raszpl/386RC-16/386RC-16 diagram.png

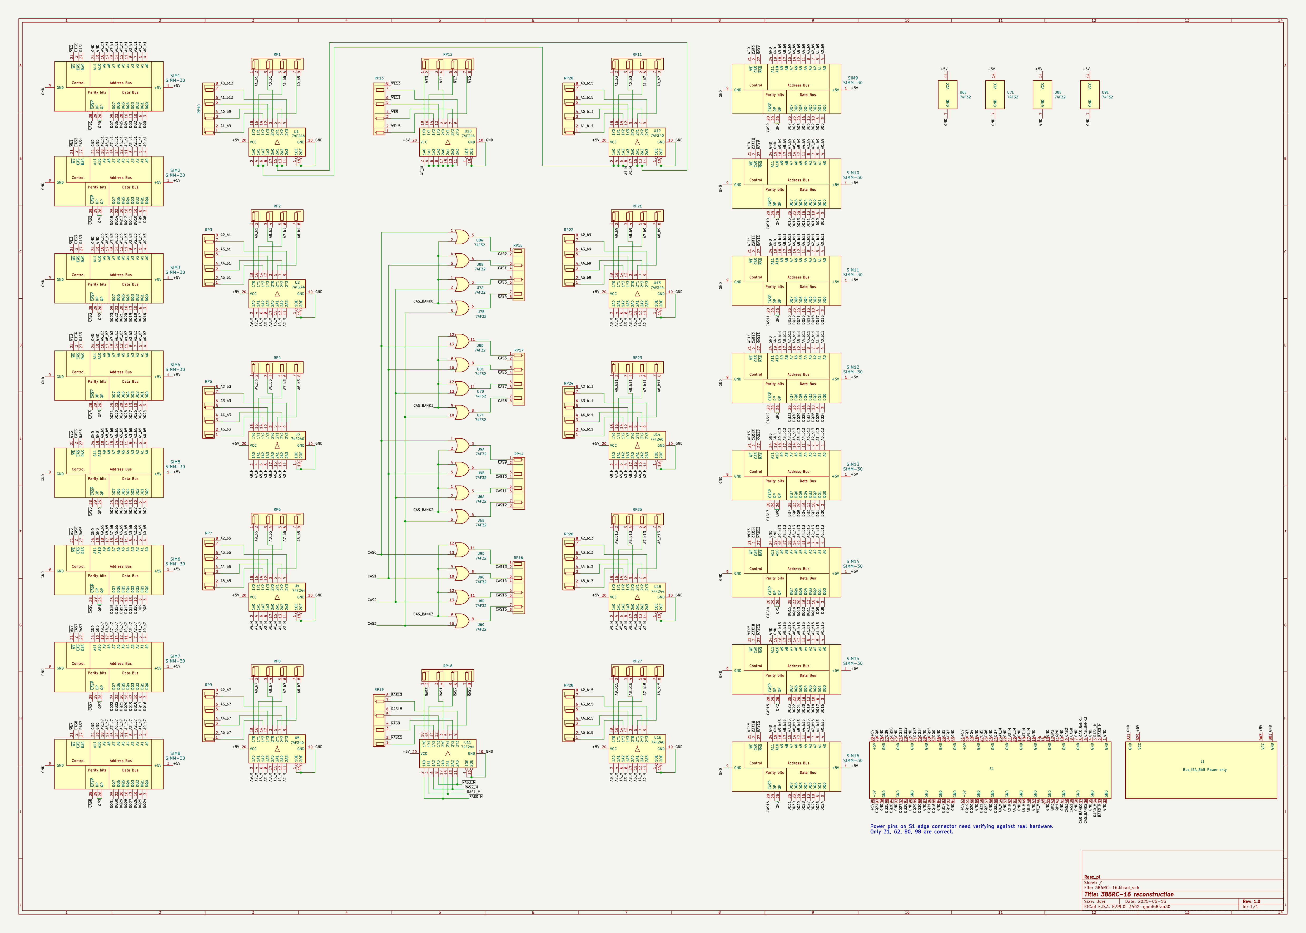
386RC-16 diagram.png
