raszpl/386RC-16/img/386RC-16 1%.jpg

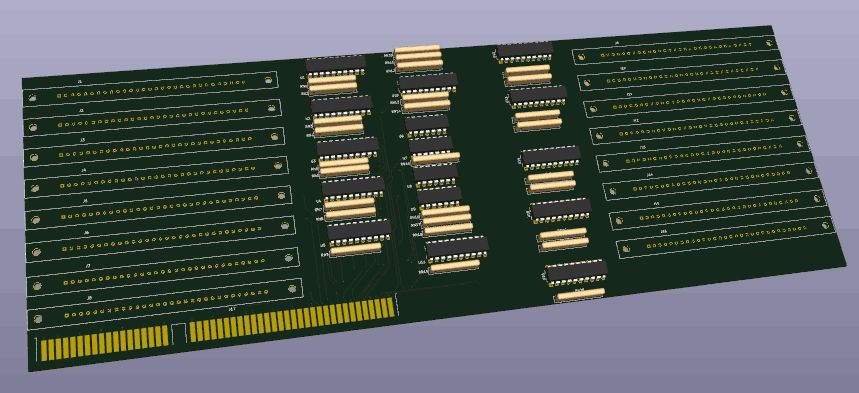
img/386RC-16 1%.jpg
