raszpl/386RC-16/img/386RC-16 95% b c.jpg

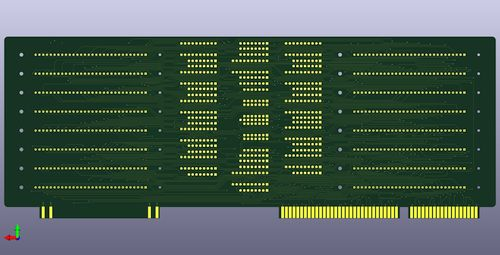
img/386RC-16 95% b c.jpg
