raszpl/386RC-16/img/386RC-16 about 10%.jpg

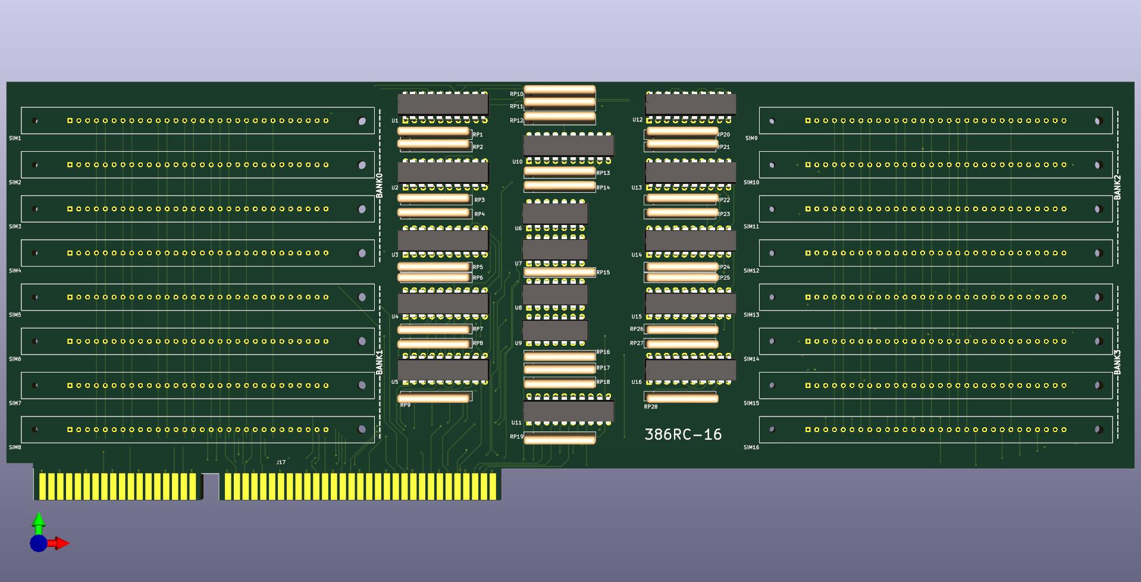
img/386RC-16 about 10%.jpg
