raszpl/386RC-16/img/386RC-16 about 10%b.jpg

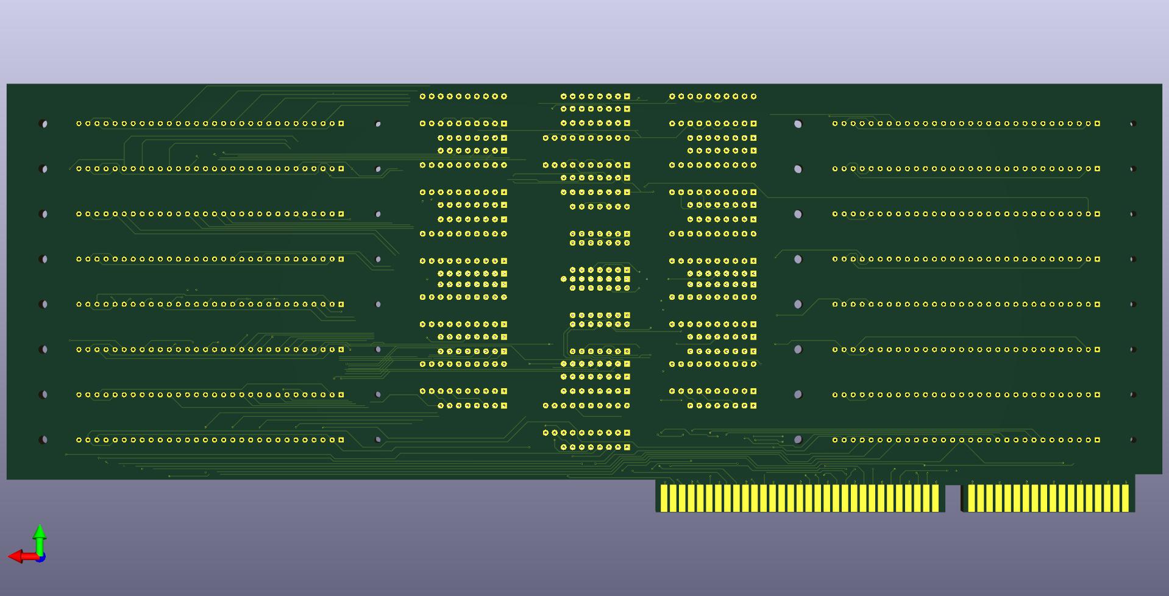
img/386RC-16 about 10%b.jpg
