raszpl/386RC-16/386RC-16.kicad_sch

## KiCad design 386RC-16.kicad_sch (2025-05-15)

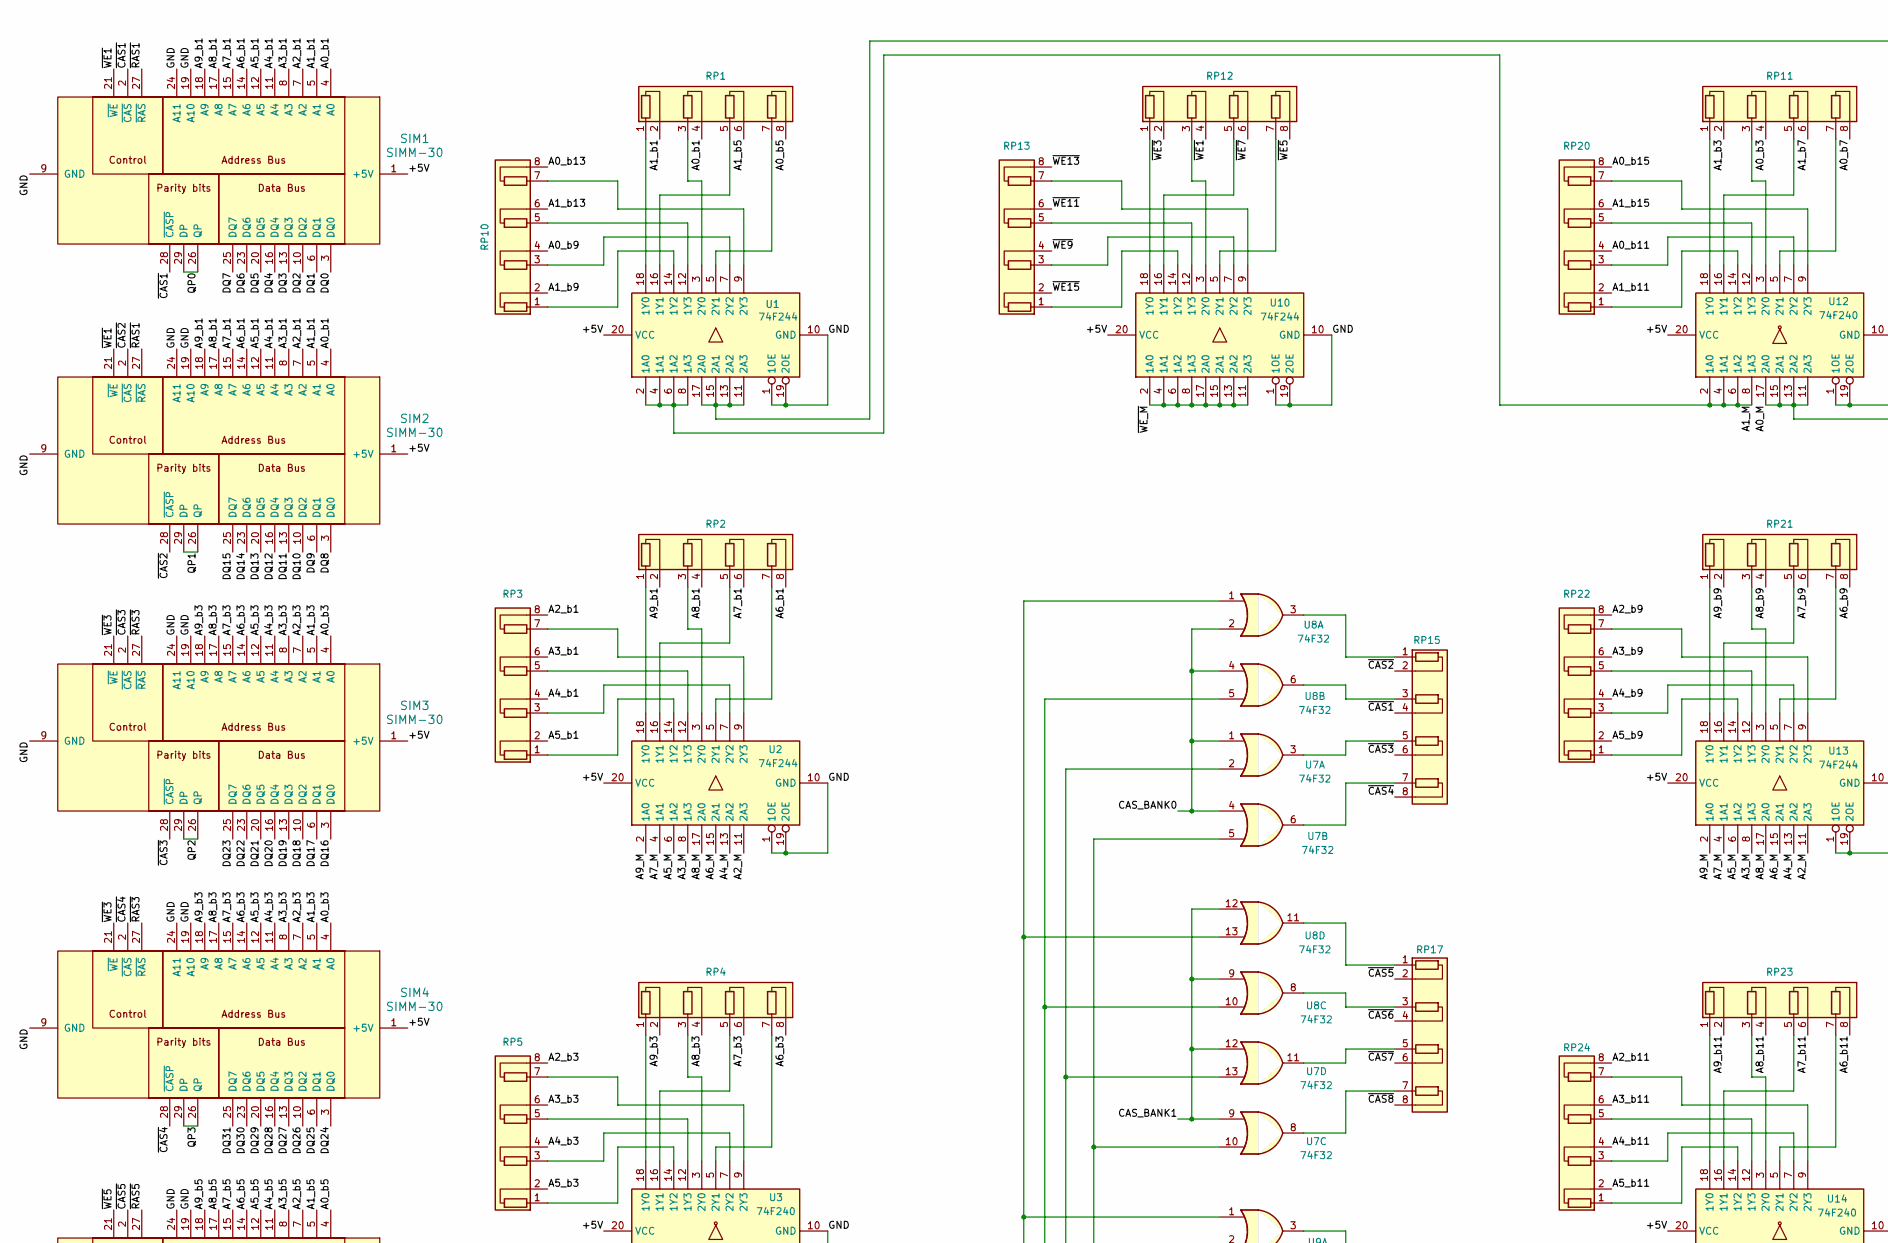
[picture p23: schematic 386RC-16.kicad_sch, part in row 1, column 1]

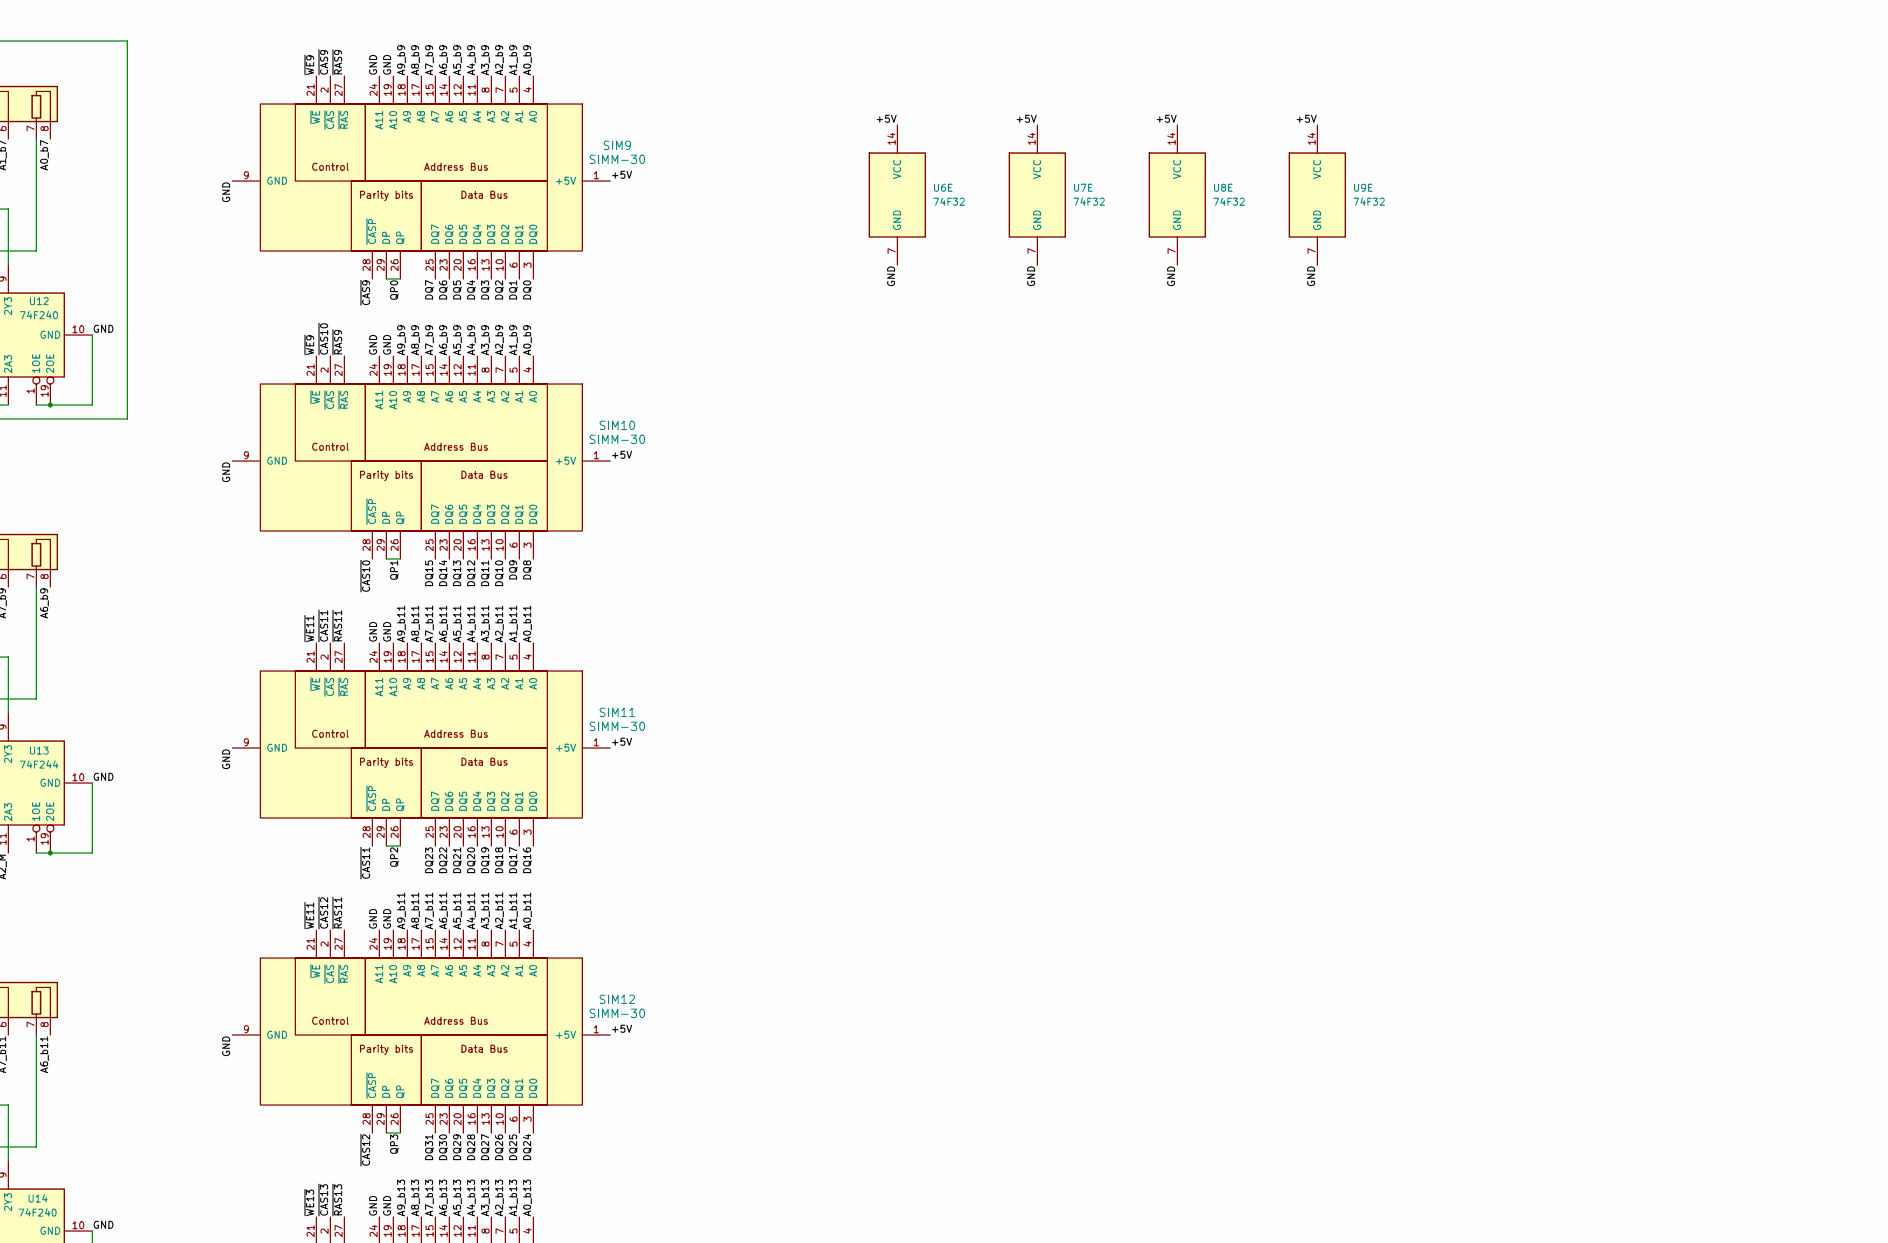
[picture p24: schematic 386RC-16.kicad_sch, part in row 1, column 2]

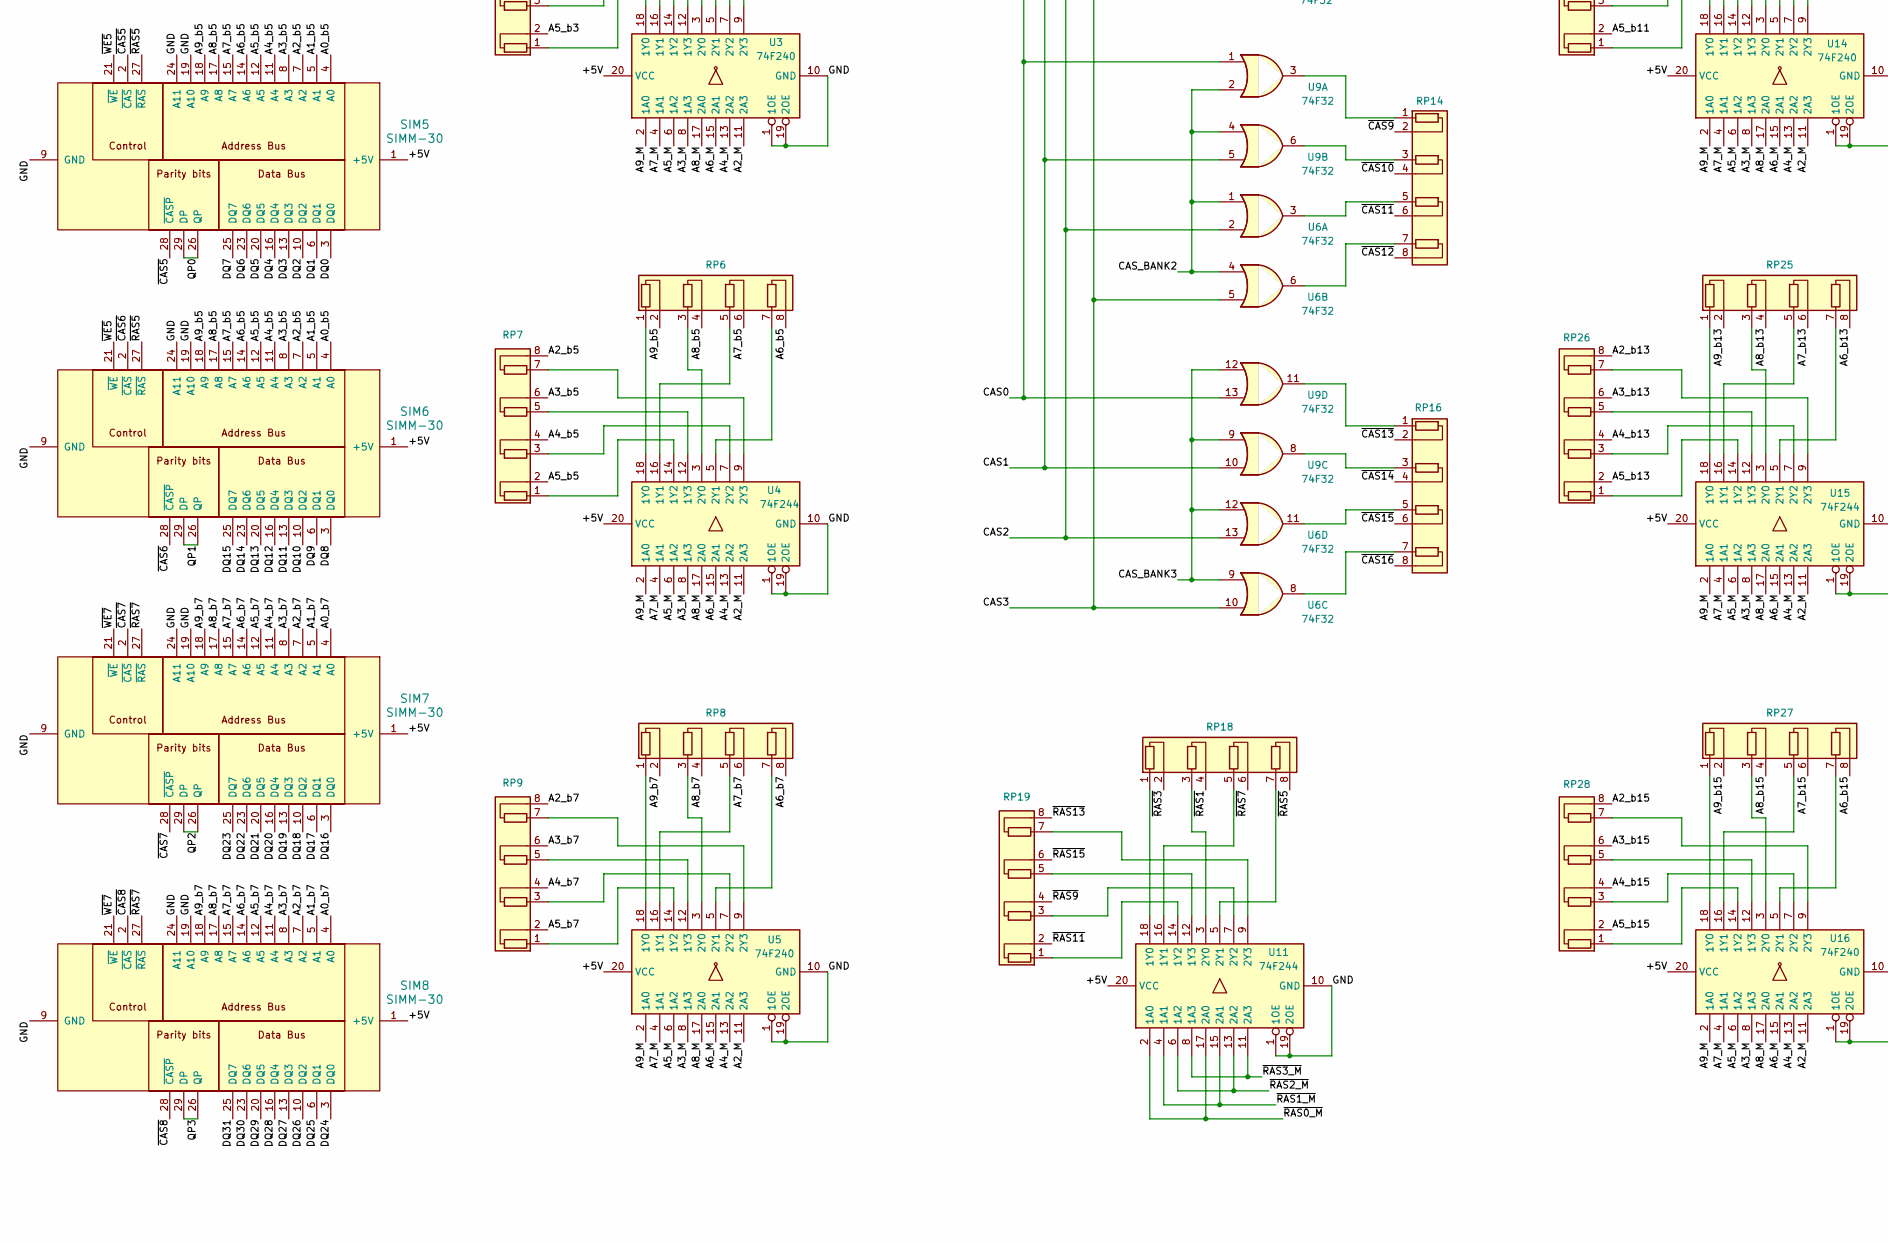
[picture p25: schematic 386RC-16.kicad_sch, part in row 2, column 1]

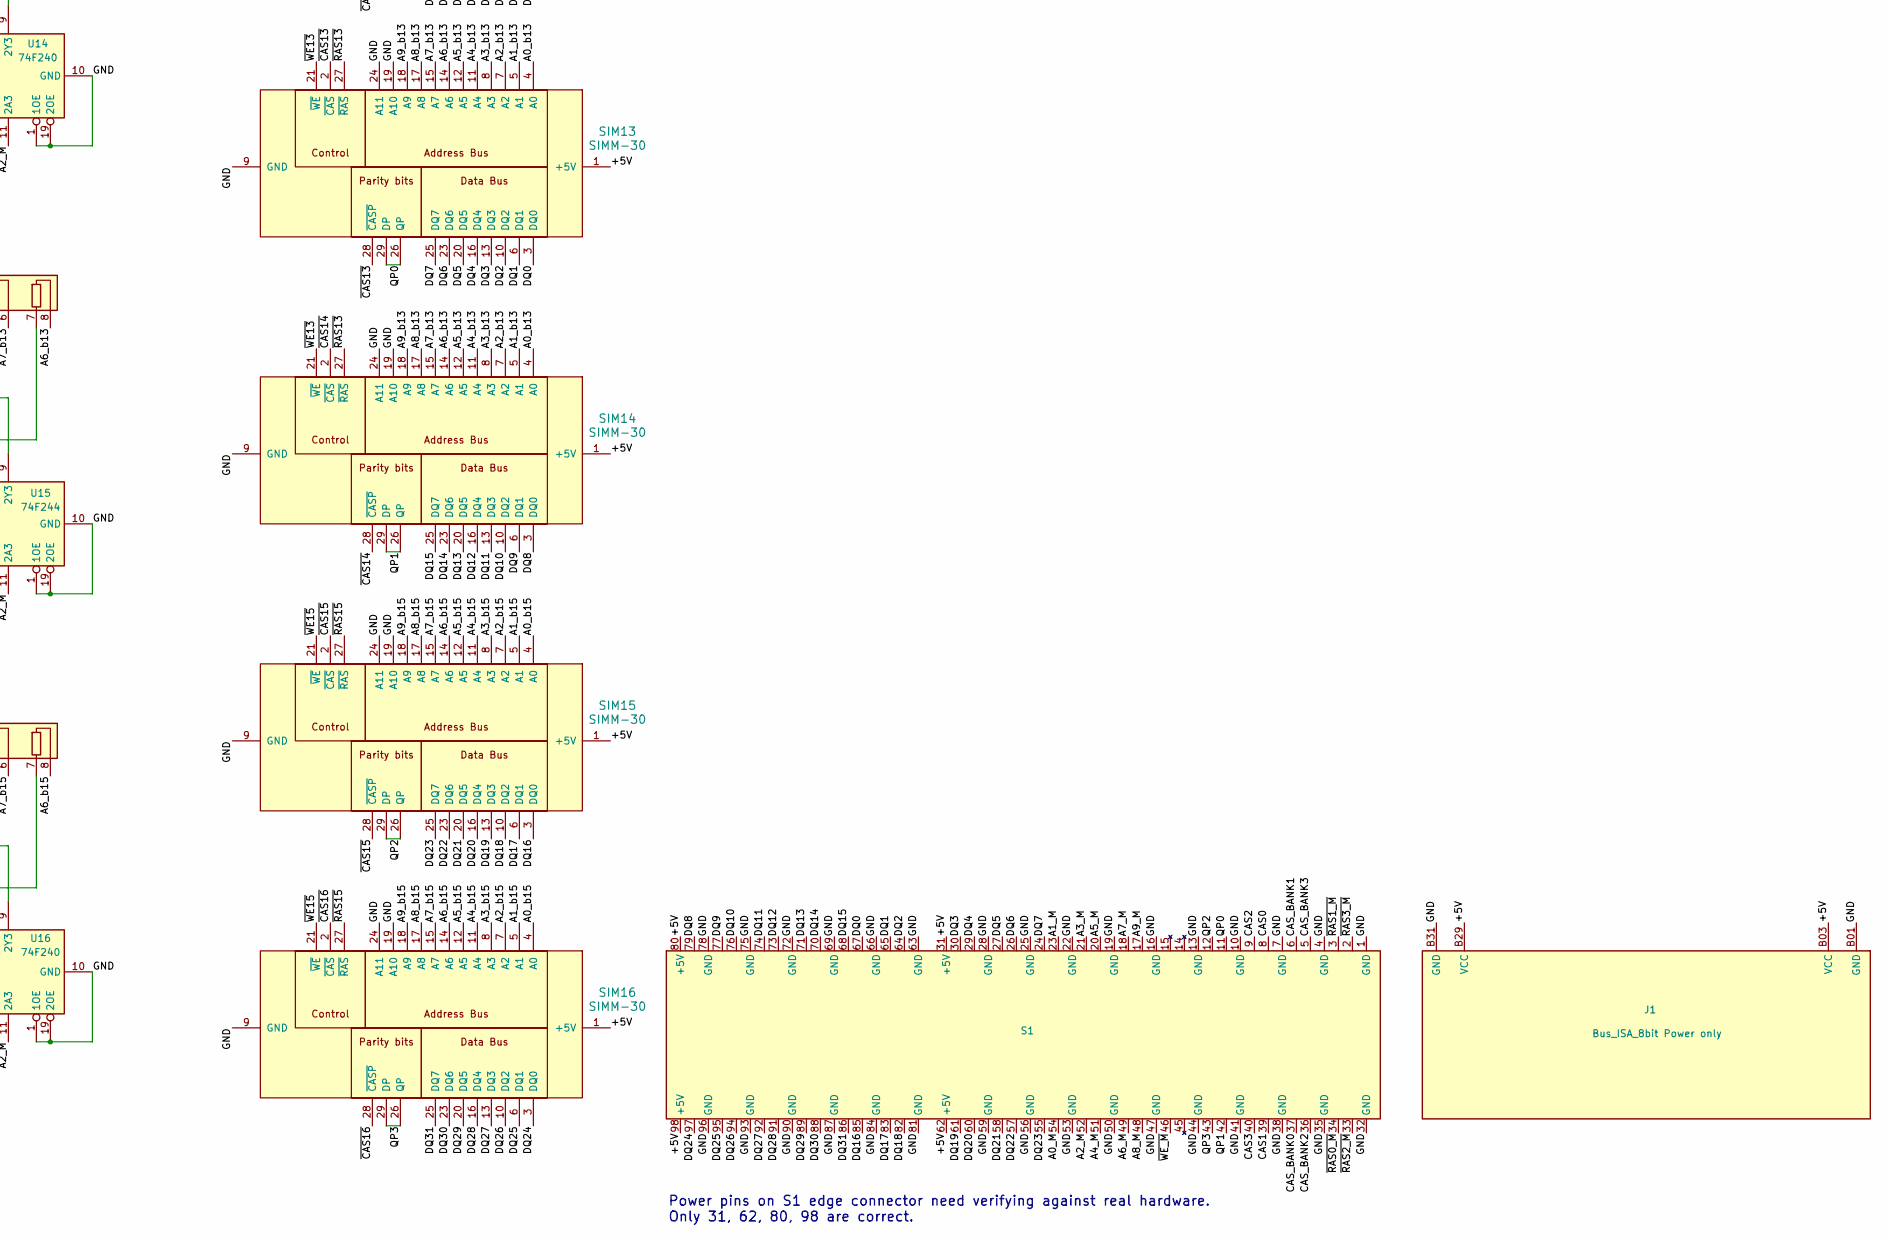
[picture p26: schematic 386RC-16.kicad_sch, part in row 2, column 2]

Parts:
J1: Bus_ISA_8bit Power only; ISA Power only
RP1, RP10, RP11, RP12, RP13, RP14, RP15, RP16, RP17, RP18, RP19, RP20, RP21, RP22, RP23, RP24, RP25, RP26, RP27, RP28: 22 Ohm; R_Array_SIP8
RP2, RP3, RP4, RP5, RP6, RP7, RP8, RP9: 22Ohm; R_Array_SIP8
S1: Bus_ISA_16bit; BUS_AT
SIM1, SIM2, SIM3, SIM4, SIM5, SIM6, SIM7, SIM8, SIM9, SIM10, SIM11, SIM12, SIM13, SIM14, SIM15, SIM16: SIMM-30; SIMM
U1, U2, U4, U10, U11, U13, U15: 74F244; DIP-20_W7.62mm
U3, U5, U12, U14, U16: 74F240; DIP-20_W7.62mm
U6, U7, U8, U9: 74F32; DIP-14_W7.62mm

Connections:
+5V: J1.B03 (VCC), J1.B29 (VCC), S1.31 (+5V), S1.62 (+5V), S1.80 (+5V), S1.98 (+5V), SIM1.1 (+5V), SIM1.30 (+5V), SIM2.1 (+5V), SIM2.30 (+5V), SIM3.1 (+5V), SIM3.30 (+5V), SIM4.1 (+5V), SIM4.30 (+5V), SIM5.1 (+5V), SIM5.30 (+5V), SIM6.1 (+5V), SIM6.30 (+5V), SIM7.1 (+5V), SIM7.30 (+5V), SIM8.1 (+5V), SIM8.30 (+5V), SIM9.1 (+5V), SIM9.30 (+5V), SIM10.1 (+5V), SIM10.30 (+5V), SIM11.1 (+5V), SIM11.30 (+5V), SIM12.1 (+5V), SIM12.30 (+5V), SIM13.1 (+5V), SIM13.30 (+5V), SIM14.1 (+5V), SIM14.30 (+5V), SIM15.1 (+5V), SIM15.30 (+5V), SIM16.1 (+5V), SIM16.30 (+5V), U1.20 (VCC), U2.20 (VCC), U3.20 (VCC), U4.20 (VCC), U5.20 (VCC), U6.14 (VCC), U7.14 (VCC), U8.14 (VCC), U9.14 (VCC), U10.20 (VCC), U11.20 (VCC), U12.20 (VCC), U13.20 (VCC), U14.20 (VCC), U15.20 (VCC), U16.20 (VCC)
A0_M: S1.54, U1.11 (2A3), U1.13 (2A2), U1.15 (2A1), U1.17 (2A0), U12.11 (2A3), U12.13 (2A2), U12.15 (2A1), U12.17 (2A0)
A0_b1: RP1.4 (R2.2), SIM1.4 (A0), SIM2.4 (A0)
A0_b3: RP11.4 (R2.2), SIM3.4 (A0), SIM4.4 (A0)
A0_b5: RP1.8 (R4.2), SIM5.4 (A0), SIM6.4 (A0)
A0_b7: RP11.8 (R4.2), SIM7.4 (A0), SIM8.4 (A0)
A0_b9: RP10.4 (R2.2), SIM9.4 (A0), SIM10.4 (A0)
A0_b11: RP20.4 (R2.2), SIM11.4 (A0), SIM12.4 (A0)
A0_b13: RP10.8 (R4.2), SIM13.4 (A0), SIM14.4 (A0)
A0_b15: RP20.8 (R4.2), SIM15.4 (A0), SIM16.4 (A0)
A1_M: S1.23, U1.2 (1A0), U1.4 (1A1), U1.6 (1A2), U1.8 (1A3), U12.2 (1A0), U12.4 (1A1), U12.6 (1A2), U12.8 (1A3)
A1_b1: RP1.2 (R1.2), SIM1.5 (A1), SIM2.5 (A1)
A1_b3: RP11.2 (R1.2), SIM3.5 (A1), SIM4.5 (A1)
A1_b5: RP1.6 (R3.2), SIM5.5 (A1), SIM6.5 (A1)
A1_b7: RP11.6 (R3.2), SIM7.5 (A1), SIM8.5 (A1)
A1_b9: RP10.2 (R1.2), SIM9.5 (A1), SIM10.5 (A1)
A1_b11: RP20.2 (R1.2), SIM11.5 (A1), SIM12.5 (A1)
A1_b13: RP10.6 (R3.2), SIM13.5 (A1), SIM14.5 (A1)
A1_b15: RP20.6 (R3.2), SIM15.5 (A1), SIM16.5 (A1)
A2_M: S1.52, U2.11 (2A3), U3.11 (2A3), U4.11 (2A3), U5.11 (2A3), U13.11 (2A3), U14.11 (2A3), U15.11 (2A3), U16.11 (2A3)
A2_b1: RP3.8 (R4.2), SIM1.7 (A2), SIM2.7 (A2)
A2_b3: RP5.8 (R4.2), SIM3.7 (A2), SIM4.7 (A2)
A2_b5: RP7.8 (R4.2), SIM5.7 (A2), SIM6.7 (A2)
A2_b7: RP9.8 (R4.2), SIM7.7 (A2), SIM8.7 (A2)
A2_b9: RP22.8 (R4.2), SIM9.7 (A2), SIM10.7 (A2)
A2_b11: RP24.8 (R4.2), SIM11.7 (A2), SIM12.7 (A2)
A2_b13: RP26.8 (R4.2), SIM13.7 (A2), SIM14.7 (A2)
A2_b15: RP28.8 (R4.2), SIM15.7 (A2), SIM16.7 (A2)
A3_M: S1.21, U2.8 (1A3), U3.8 (1A3), U4.8 (1A3), U5.8 (1A3), U13.8 (1A3), U14.8 (1A3), U15.8 (1A3), U16.8 (1A3)
A3_b1: RP3.6 (R3.2), SIM1.8 (A3), SIM2.8 (A3)
A3_b3: RP5.6 (R3.2), SIM3.8 (A3), SIM4.8 (A3)
A3_b5: RP7.6 (R3.2), SIM5.8 (A3), SIM6.8 (A3)
A3_b7: RP9.6 (R3.2), SIM7.8 (A3), SIM8.8 (A3)
A3_b9: RP22.6 (R3.2), SIM9.8 (A3), SIM10.8 (A3)
A3_b11: RP24.6 (R3.2), SIM11.8 (A3), SIM12.8 (A3)
A3_b13: RP26.6 (R3.2), SIM13.8 (A3), SIM14.8 (A3)
A3_b15: RP28.6 (R3.2), SIM15.8 (A3), SIM16.8 (A3)
A4_M: S1.51, U2.13 (2A2), U3.13 (2A2), U4.13 (2A2), U5.13 (2A2), U13.13 (2A2), U14.13 (2A2), U15.13 (2A2), U16.13 (2A2)
A4_b1: RP3.4 (R2.2), SIM1.11 (A4), SIM2.11 (A4)
A4_b3: RP5.4 (R2.2), SIM3.11 (A4), SIM4.11 (A4)
A4_b5: RP7.4 (R2.2), SIM5.11 (A4), SIM6.11 (A4)
A4_b7: RP9.4 (R2.2), SIM7.11 (A4), SIM8.11 (A4)
A4_b9: RP22.4 (R2.2), SIM9.11 (A4), SIM10.11 (A4)
A4_b11: RP24.4 (R2.2), SIM11.11 (A4), SIM12.11 (A4)
A4_b13: RP26.4 (R2.2), SIM13.11 (A4), SIM14.11 (A4)
A4_b15: RP28.4 (R2.2), SIM15.11 (A4), SIM16.11 (A4)
A5_M: S1.20, U2.6 (1A2), U3.6 (1A2), U4.6 (1A2), U5.6 (1A2), U13.6 (1A2), U14.6 (1A2), U15.6 (1A2), U16.6 (1A2)
A5_b1: RP3.2 (R1.2), SIM1.12 (A5), SIM2.12 (A5)
A5_b3: RP5.2 (R1.2), SIM3.12 (A5), SIM4.12 (A5)
A5_b5: RP7.2 (R1.2), SIM5.12 (A5), SIM6.12 (A5)
A5_b7: RP9.2 (R1.2), SIM7.12 (A5), SIM8.12 (A5)
A5_b9: RP22.2 (R1.2), SIM9.12 (A5), SIM10.12 (A5)
A5_b11: RP24.2 (R1.2), SIM11.12 (A5), SIM12.12 (A5)
A5_b13: RP26.2 (R1.2), SIM13.12 (A5), SIM14.12 (A5)
A5_b15: RP28.2 (R1.2), SIM15.12 (A5), SIM16.12 (A5)
A6_M: S1.49, U2.15 (2A1), U3.15 (2A1), U4.15 (2A1), U5.15 (2A1), U13.15 (2A1), U14.15 (2A1), U15.15 (2A1), U16.15 (2A1)
A6_b1: RP2.8 (R4.2), SIM1.14 (A6), SIM2.14 (A6)
A6_b3: RP4.8 (R4.2), SIM3.14 (A6), SIM4.14 (A6)
A6_b5: RP6.8 (R4.2), SIM5.14 (A6), SIM6.14 (A6)
A6_b7: RP8.8 (R4.2), SIM7.14 (A6), SIM8.14 (A6)
A6_b9: RP21.8 (R4.2), SIM9.14 (A6), SIM10.14 (A6)
A6_b11: RP23.8 (R4.2), SIM11.14 (A6), SIM12.14 (A6)
A6_b13: RP25.8 (R4.2), SIM13.14 (A6), SIM14.14 (A6)
A6_b15: RP27.8 (R4.2), SIM15.14 (A6), SIM16.14 (A6)
A7_M: S1.18, U2.4 (1A1), U3.4 (1A1), U4.4 (1A1), U5.4 (1A1), U13.4 (1A1), U14.4 (1A1), U15.4 (1A1), U16.4 (1A1)
A7_b1: RP2.6 (R3.2), SIM1.15 (A7), SIM2.15 (A7)
A7_b3: RP4.6 (R3.2), SIM3.15 (A7), SIM4.15 (A7)
A7_b5: RP6.6 (R3.2), SIM5.15 (A7), SIM6.15 (A7)
A7_b7: RP8.6 (R3.2), SIM7.15 (A7), SIM8.15 (A7)
A7_b9: RP21.6 (R3.2), SIM9.15 (A7), SIM10.15 (A7)
A7_b11: RP23.6 (R3.2), SIM11.15 (A7), SIM12.15 (A7)
A7_b13: RP25.6 (R3.2), SIM13.15 (A7), SIM14.15 (A7)
A7_b15: RP27.6 (R3.2), SIM15.15 (A7), SIM16.15 (A7)
A8_M: S1.48, U2.17 (2A0), U3.17 (2A0), U4.17 (2A0), U5.17 (2A0), U13.17 (2A0), U14.17 (2A0), U15.17 (2A0), U16.17 (2A0)
A8_b1: RP2.4 (R2.2), SIM1.17 (A8), SIM2.17 (A8)
A8_b3: RP4.4 (R2.2), SIM3.17 (A8), SIM4.17 (A8)
A8_b5: RP6.4 (R2.2), SIM5.17 (A8), SIM6.17 (A8)
A8_b7: RP8.4 (R2.2), SIM7.17 (A8), SIM8.17 (A8)
A8_b9: RP21.4 (R2.2), SIM9.17 (A8), SIM10.17 (A8)
A8_b11: RP23.4 (R2.2), SIM11.17 (A8), SIM12.17 (A8)
A8_b13: RP25.4 (R2.2), SIM13.17 (A8), SIM14.17 (A8)
A8_b15: RP27.4 (R2.2), SIM15.17 (A8), SIM16.17 (A8)
A9_M: S1.17, U2.2 (1A0), U3.2 (1A0), U4.2 (1A0), U5.2 (1A0), U13.2 (1A0), U14.2 (1A0), U15.2 (1A0), U16.2 (1A0)
A9_b1: RP2.2 (R1.2), SIM1.18 (A9), SIM2.18 (A9)
A9_b3: RP4.2 (R1.2), SIM3.18 (A9), SIM4.18 (A9)
A9_b5: RP6.2 (R1.2), SIM5.18 (A9), SIM6.18 (A9)
A9_b7: RP8.2 (R1.2), SIM7.18 (A9), SIM8.18 (A9)
A9_b9: RP21.2 (R1.2), SIM9.18 (A9), SIM10.18 (A9)
A9_b11: RP23.2 (R1.2), SIM11.18 (A9), SIM12.18 (A9)
A9_b13: RP25.2 (R1.2), SIM13.18 (A9), SIM14.18 (A9)
A9_b15: RP27.2 (R1.2), SIM15.18 (A9), SIM16.18 (A9)
CAS0: S1.8, U8.1, U8.13, U9.1, U9.13
CAS1: S1.39, U8.5, U8.10, U9.5, U9.10
CAS2: S1.9, U6.2, U6.13, U7.2, U7.13
CAS3: S1.40, U6.5, U6.10, U7.5, U7.10
CAS_BANK0: S1.37, U7.1, U7.4, U8.2, U8.4
CAS_BANK1: S1.6, U7.9, U7.12, U8.9, U8.12
CAS_BANK2: S1.36, U6.1, U6.4, U9.2, U9.4
CAS_BANK3: S1.5, U6.9, U6.12, U9.9, U9.12
DQ0: S1.67, SIM1.3 (DQ0), SIM5.3 (DQ0), SIM9.3 (DQ0), SIM13.3 (DQ0)
DQ1: S1.65, SIM1.6 (DQ1), SIM5.6 (DQ1), SIM9.6 (DQ1), SIM13.6 (DQ1)
DQ2: S1.64, SIM1.10 (DQ2), SIM5.10 (DQ2), SIM9.10 (DQ2), SIM13.10 (DQ2)
DQ3: S1.30, SIM1.13 (DQ3), SIM5.13 (DQ3), SIM9.13 (DQ3), SIM13.13 (DQ3)
DQ4: S1.29, SIM1.16 (DQ4), SIM5.16 (DQ4), SIM9.16 (DQ4), SIM13.16 (DQ4)
DQ5: S1.27, SIM1.20 (DQ5), SIM5.20 (DQ5), SIM9.20 (DQ5), SIM13.20 (DQ5)
DQ6: S1.26, SIM1.23 (DQ6), SIM5.23 (DQ6), SIM9.23 (DQ6), SIM13.23 (DQ6)
DQ7: S1.24, SIM1.25 (DQ7), SIM5.25 (DQ7), SIM9.25 (DQ7), SIM13.25 (DQ7)
DQ8: S1.79, SIM2.3 (DQ0), SIM6.3 (DQ0), SIM10.3 (DQ0), SIM14.3 (DQ0)
DQ9: S1.77, SIM2.6 (DQ1), SIM6.6 (DQ1), SIM10.6 (DQ1), SIM14.6 (DQ1)
DQ10: S1.76, SIM2.10 (DQ2), SIM6.10 (DQ2), SIM10.10 (DQ2), SIM14.10 (DQ2)
DQ11: S1.74, SIM2.13 (DQ3), SIM6.13 (DQ3), SIM10.13 (DQ3), SIM14.13 (DQ3)
DQ12: S1.73, SIM2.16 (DQ4), SIM6.16 (DQ4), SIM10.16 (DQ4), SIM14.16 (DQ4)
DQ13: S1.71, SIM2.20 (DQ5), SIM6.20 (DQ5), SIM10.20 (DQ5), SIM14.20 (DQ5)
DQ14: S1.70, SIM2.23 (DQ6), SIM6.23 (DQ6), SIM10.23 (DQ6), SIM14.23 (DQ6)
DQ15: S1.68, SIM2.25 (DQ7), SIM6.25 (DQ7), SIM10.25 (DQ7), SIM14.25 (DQ7)
DQ16: S1.85, SIM3.3 (DQ0), SIM7.3 (DQ0), SIM11.3 (DQ0), SIM15.3 (DQ0)
DQ17: S1.83, SIM3.6 (DQ1), SIM7.6 (DQ1), SIM11.6 (DQ1), SIM15.6 (DQ1)
DQ18: S1.82, SIM3.10 (DQ2), SIM7.10 (DQ2), SIM11.10 (DQ2), SIM15.10 (DQ2)
DQ19: S1.61, SIM3.13 (DQ3), SIM7.13 (DQ3), SIM11.13 (DQ3), SIM15.13 (DQ3)
DQ20: S1.60, SIM3.16 (DQ4), SIM7.16 (DQ4), SIM11.16 (DQ4), SIM15.16 (DQ4)
DQ21: S1.58, SIM3.20 (DQ5), SIM7.20 (DQ5), SIM11.20 (DQ5), SIM15.20 (DQ5)
DQ22: S1.57, SIM3.23 (DQ6), SIM7.23 (DQ6), SIM11.23 (DQ6), SIM15.23 (DQ6)
DQ23: S1.55, SIM3.25 (DQ7), SIM7.25 (DQ7), SIM11.25 (DQ7), SIM15.25 (DQ7)
DQ24: S1.97, SIM4.3 (DQ0), SIM8.3 (DQ0), SIM12.3 (DQ0), SIM16.3 (DQ0)
DQ25: S1.95, SIM4.6 (DQ1), SIM8.6 (DQ1), SIM12.6 (DQ1), SIM16.6 (DQ1)
DQ26: S1.94, SIM4.10 (DQ2), SIM8.10 (DQ2), SIM12.10 (DQ2), SIM16.10 (DQ2)
DQ27: S1.92, SIM4.13 (DQ3), SIM8.13 (DQ3), SIM12.13 (DQ3), SIM16.13 (DQ3)
DQ28: S1.91, SIM4.16 (DQ4), SIM8.16 (DQ4), SIM12.16 (DQ4), SIM16.16 (DQ4)
DQ29: S1.89, SIM4.20 (DQ5), SIM8.20 (DQ5), SIM12.20 (DQ5), SIM16.20 (DQ5)
DQ30: S1.88, SIM4.23 (DQ6), SIM8.23 (DQ6), SIM12.23 (DQ6), SIM16.23 (DQ6)
DQ31: S1.86, SIM4.25 (DQ7), SIM8.25 (DQ7), SIM12.25 (DQ7), SIM16.25 (DQ7)
GND: J1.B01 (GND), J1.B31 (GND), S1.1 (GND), S1.4 (GND), S1.7 (GND), S1.10 (GND), S1.13 (GND), S1.16 (GND), S1.19 (GND), S1.22 (GND), S1.25 (GND), S1.28 (GND), S1.32 (GND), S1.35 (GND), S1.38 (GND), S1.41 (GND), S1.44 (GND), S1.47 (GND), S1.50 (GND), S1.53 (GND), S1.56 (GND), S1.59 (GND), S1.63 (GND), S1.66 (GND), S1.69 (GND), S1.72 (GND), S1.75 (GND), S1.78 (GND), S1.81 (GND), S1.84 (GND), S1.87 (GND), S1.90 (GND), S1.93 (GND), S1.96 (GND), SIM1.9 (GND), SIM1.19 (A10), SIM1.22 (GND), SIM1.24 (A11), SIM2.9 (GND), SIM2.19 (A10), SIM2.22 (GND), SIM2.24 (A11), SIM3.9 (GND), SIM3.19 (A10), SIM3.22 (GND), SIM3.24 (A11), SIM4.9 (GND), SIM4.19 (A10), SIM4.22 (GND), SIM4.24 (A11), SIM5.9 (GND), SIM5.19 (A10), SIM5.22 (GND), SIM5.24 (A11), SIM6.9 (GND), SIM6.19 (A10), SIM6.22 (GND), SIM6.24 (A11), SIM7.9 (GND), SIM7.19 (A10), SIM7.22 (GND), SIM7.24 (A11), SIM8.9 (GND), SIM8.19 (A10), SIM8.22 (GND), SIM8.24 (A11), SIM9.9 (GND), SIM9.19 (A10), SIM9.22 (GND), SIM9.24 (A11), SIM10.9 (GND), SIM10.19 (A10), SIM10.22 (GND), SIM10.24 (A11), SIM11.9 (GND), SIM11.19 (A10), SIM11.22 (GND), SIM11.24 (A11), SIM12.9 (GND), SIM12.19 (A10), SIM12.22 (GND), SIM12.24 (A11), SIM13.9 (GND), SIM13.19 (A10), SIM13.22 (GND), SIM13.24 (A11), SIM14.9 (GND), SIM14.19 (A10), SIM14.22 (GND), SIM14.24 (A11), SIM15.9 (GND), SIM15.19 (A10), SIM15.22 (GND), SIM15.24 (A11), SIM16.9 (GND), SIM16.19 (A10), SIM16.22 (GND), SIM16.24 (A11), U1.1 (1OE), U1.10 (GND), U1.19 (2OE), U2.1 (1OE), U2.10 (GND), U2.19 (2OE), U3.1 (1OE), U3.10 (GND), U3.19 (2OE), U4.1 (1OE), U4.10 (GND), U4.19 (2OE), U5.1 (1OE), U5.10 (GND), U5.19 (2OE), U6.7 (GND), U7.7 (GND), U8.7 (GND), U9.7 (GND), U10.1 (1OE), U10.10 (GND), U10.19 (2OE), U11.1 (1OE), U11.10 (GND), U11.19 (2OE), U12.1 (1OE), U12.10 (GND), U12.19 (2OE), U13.1 (1OE), U13.10 (GND), U13.19 (2OE), U14.1 (1OE), U14.10 (GND), U14.19 (2OE), U15.1 (1OE), U15.10 (GND), U15.19 (2OE), U16.1 (1OE), U16.10 (GND), U16.19 (2OE)
unnamed: RP1.1 (R1.1), U1.18 (1Y0)
unnamed: RP1.3 (R2.1), U1.3 (2Y0)
unnamed: RP1.5 (R3.1), U1.16 (1Y1)
unnamed: RP1.7 (R4.1), U1.5 (2Y1)
unnamed: RP2.1 (R1.1), U2.18 (1Y0)
unnamed: RP2.3 (R2.1), U2.3 (2Y0)
unnamed: RP2.5 (R3.1), U2.16 (1Y1)
unnamed: RP2.7 (R4.1), U2.5 (2Y1)
unnamed: RP3.1 (R1.1), U2.14 (1Y2)
unnamed: RP3.3 (R2.1), U2.7 (2Y2)
unnamed: RP3.5 (R3.1), U2.12 (1Y3)
unnamed: RP3.7 (R4.1), U2.9 (2Y3)
unnamed: RP4.1 (R1.1), U3.18 (1Y0)
unnamed: RP4.3 (R2.1), U3.3 (2Y0)
unnamed: RP4.5 (R3.1), U3.16 (1Y1)
unnamed: RP4.7 (R4.1), U3.5 (2Y1)
unnamed: RP5.1 (R1.1), U3.14 (1Y2)
unnamed: RP5.3 (R2.1), U3.7 (2Y2)
unnamed: RP5.5 (R3.1), U3.12 (1Y3)
unnamed: RP5.7 (R4.1), U3.9 (2Y3)
unnamed: RP6.1 (R1.1), U4.18 (1Y0)
unnamed: RP6.3 (R2.1), U4.3 (2Y0)
unnamed: RP6.5 (R3.1), U4.16 (1Y1)
unnamed: RP6.7 (R4.1), U4.5 (2Y1)
unnamed: RP7.1 (R1.1), U4.14 (1Y2)
unnamed: RP7.3 (R2.1), U4.7 (2Y2)
unnamed: RP7.5 (R3.1), U4.12 (1Y3)
unnamed: RP7.7 (R4.1), U4.9 (2Y3)
unnamed: RP8.1 (R1.1), U5.18 (1Y0)
unnamed: RP8.3 (R2.1), U5.3 (2Y0)
unnamed: RP8.5 (R3.1), U5.16 (1Y1)
unnamed: RP8.7 (R4.1), U5.5 (2Y1)
unnamed: RP9.1 (R1.1), U5.14 (1Y2)
unnamed: RP9.3 (R2.1), U5.7 (2Y2)
unnamed: RP9.5 (R3.1), U5.12 (1Y3)
unnamed: RP9.7 (R4.1), U5.9 (2Y3)
unnamed: RP10.1 (R1.1), U1.14 (1Y2)
unnamed: RP10.3 (R2.1), U1.7 (2Y2)
unnamed: RP10.5 (R3.1), U1.12 (1Y3)
unnamed: RP10.7 (R4.1), U1.9 (2Y3)
unnamed: RP11.1 (R1.1), U12.18 (1Y0)
unnamed: RP11.3 (R2.1), U12.3 (2Y0)
unnamed: RP11.5 (R3.1), U12.16 (1Y1)
unnamed: RP11.7 (R4.1), U12.5 (2Y1)
unnamed: RP12.1 (R1.1), U10.18 (1Y0)
unnamed: RP12.3 (R2.1), U10.3 (2Y0)
unnamed: RP12.5 (R3.1), U10.16 (1Y1)
unnamed: RP12.7 (R4.1), U10.5 (2Y1)
unnamed: RP13.1 (R1.1), U10.14 (1Y2)
unnamed: RP13.3 (R2.1), U10.7 (2Y2)
unnamed: RP13.5 (R3.1), U10.12 (1Y3)
unnamed: RP13.7 (R4.1), U10.9 (2Y3)
unnamed: RP14.1 (R1.1), U9.3
unnamed: RP14.3 (R2.1), U9.6
unnamed: RP14.5 (R3.1), U6.3
unnamed: RP14.7 (R4.1), U6.6
unnamed: RP15.1 (R1.1), U8.3
unnamed: RP15.3 (R2.1), U8.6
unnamed: RP15.5 (R3.1), U7.3
unnamed: RP15.7 (R4.1), U7.6
unnamed: RP16.1 (R1.1), U9.11
unnamed: RP16.3 (R2.1), U9.8
unnamed: RP16.5 (R3.1), U6.11
unnamed: RP16.7 (R4.1), U6.8
unnamed: RP17.1 (R1.1), U8.11
unnamed: RP17.3 (R2.1), U8.8
unnamed: RP17.5 (R3.1), U7.11
unnamed: RP17.7 (R4.1), U7.8
unnamed: RP18.1 (R1.1), U11.18 (1Y0)
unnamed: RP18.3 (R2.1), U11.3 (2Y0)
unnamed: RP18.5 (R3.1), U11.16 (1Y1)
unnamed: RP18.7 (R4.1), U11.5 (2Y1)
unnamed: RP19.1 (R1.1), U11.14 (1Y2)
unnamed: RP19.3 (R2.1), U11.7 (2Y2)
unnamed: RP19.5 (R3.1), U11.12 (1Y3)
unnamed: RP19.7 (R4.1), U11.9 (2Y3)
unnamed: RP20.1 (R1.1), U12.14 (1Y2)
unnamed: RP20.3 (R2.1), U12.7 (2Y2)
unnamed: RP20.5 (R3.1), U12.12 (1Y3)
unnamed: RP20.7 (R4.1), U12.9 (2Y3)
unnamed: RP21.1 (R1.1), U13.18 (1Y0)
unnamed: RP21.3 (R2.1), U13.3 (2Y0)
unnamed: RP21.5 (R3.1), U13.16 (1Y1)
unnamed: RP21.7 (R4.1), U13.5 (2Y1)
unnamed: RP22.1 (R1.1), U13.14 (1Y2)
unnamed: RP22.3 (R2.1), U13.7 (2Y2)
unnamed: RP22.5 (R3.1), U13.12 (1Y3)
unnamed: RP22.7 (R4.1), U13.9 (2Y3)
unnamed: RP23.1 (R1.1), U14.18 (1Y0)
unnamed: RP23.3 (R2.1), U14.3 (2Y0)
unnamed: RP23.5 (R3.1), U14.16 (1Y1)
unnamed: RP23.7 (R4.1), U14.5 (2Y1)
unnamed: RP24.1 (R1.1), U14.14 (1Y2)
unnamed: RP24.3 (R2.1), U14.7 (2Y2)
unnamed: RP24.5 (R3.1), U14.12 (1Y3)
unnamed: RP24.7 (R4.1), U14.9 (2Y3)
unnamed: RP25.1 (R1.1), U15.18 (1Y0)
unnamed: RP25.3 (R2.1), U15.3 (2Y0)
unnamed: RP25.5 (R3.1), U15.16 (1Y1)
unnamed: RP25.7 (R4.1), U15.5 (2Y1)
unnamed: RP26.1 (R1.1), U15.14 (1Y2)
unnamed: RP26.3 (R2.1), U15.7 (2Y2)
unnamed: RP26.5 (R3.1), U15.12 (1Y3)
unnamed: RP26.7 (R4.1), U15.9 (2Y3)
unnamed: RP27.1 (R1.1), U16.18 (1Y0)
unnamed: RP27.3 (R2.1), U16.3 (2Y0)
unnamed: RP27.5 (R3.1), U16.16 (1Y1)
unnamed: RP27.7 (R4.1), U16.5 (2Y1)
unnamed: RP28.1 (R1.1), U16.14 (1Y2)
unnamed: RP28.3 (R2.1), U16.7 (2Y2)
unnamed: RP28.5 (R3.1), U16.12 (1Y3)
unnamed: RP28.7 (R4.1), U16.9 (2Y3)
QP0: S1.11, SIM1.26 (QP), SIM1.29 (DP), SIM5.26 (QP), SIM5.29 (DP), SIM9.26 (QP), SIM9.29 (DP), SIM13.26 (QP), SIM13.29 (DP)
QP1: S1.42, SIM2.26 (QP), SIM2.29 (DP), SIM6.26 (QP), SIM6.29 (DP), SIM10.26 (QP), SIM10.29 (DP), SIM14.26 (QP), SIM14.29 (DP)
QP2: S1.12, SIM3.26 (QP), SIM3.29 (DP), SIM7.26 (QP), SIM7.29 (DP), SIM11.26 (QP), SIM11.29 (DP), SIM15.26 (QP), SIM15.29 (DP)
QP3: S1.43, SIM4.26 (QP), SIM4.29 (DP), SIM8.26 (QP), SIM8.29 (DP), SIM12.26 (QP), SIM12.29 (DP), SIM16.26 (QP), SIM16.29 (DP)
~CAS1: RP15.4 (R2.2), SIM1.2 (~CAS), SIM1.28 (~CASP)
~CAS2: RP15.2 (R1.2), SIM2.2 (~CAS), SIM2.28 (~CASP)
~CAS3: RP15.6 (R3.2), SIM3.2 (~CAS), SIM3.28 (~CASP)
~CAS4: RP15.8 (R4.2), SIM4.2 (~CAS), SIM4.28 (~CASP)
~CAS5: RP17.2 (R1.2), SIM5.2 (~CAS), SIM5.28 (~CASP)
~CAS6: RP17.4 (R2.2), SIM6.2 (~CAS), SIM6.28 (~CASP)
~CAS7: RP17.6 (R3.2), SIM7.2 (~CAS), SIM7.28 (~CASP)
~CAS8: RP17.8 (R4.2), SIM8.2 (~CAS), SIM8.28 (~CASP)
~CAS9: RP14.2 (R1.2), SIM9.2 (~CAS), SIM9.28 (~CASP)
~CAS10: RP14.4 (R2.2), SIM10.2 (~CAS), SIM10.28 (~CASP)
~CAS11: RP14.6 (R3.2), SIM11.2 (~CAS), SIM11.28 (~CASP)
~CAS12: RP14.8 (R4.2), SIM12.2 (~CAS), SIM12.28 (~CASP)
~CAS13: RP16.2 (R1.2), SIM13.2 (~CAS), SIM13.28 (~CASP)
~CAS14: RP16.4 (R2.2), SIM14.2 (~CAS), SIM14.28 (~CASP)
~CAS15: RP16.6 (R3.2), SIM15.2 (~CAS), SIM15.28 (~CASP)
~CAS16: RP16.8 (R4.2), SIM16.2 (~CAS), SIM16.28 (~CASP)
~RAS0_M: S1.34, U11.2 (1A0), U11.17 (2A0)
~RAS1_M: S1.3, U11.4 (1A1), U11.15 (2A1)
~RAS1: RP18.4 (R2.2), SIM1.27 (~RAS), SIM2.27 (~RAS)
~RAS2_M: S1.33, U11.6 (1A2), U11.13 (2A2)
~RAS3_M: S1.2, U11.8 (1A3), U11.11 (2A3)
~RAS3: RP18.2 (R1.2), SIM3.27 (~RAS), SIM4.27 (~RAS)
~RAS5: RP18.8 (R4.2), SIM5.27 (~RAS), SIM6.27 (~RAS)
~RAS7: RP18.6 (R3.2), SIM7.27 (~RAS), SIM8.27 (~RAS)
~RAS9: RP19.4 (R2.2), SIM9.27 (~RAS), SIM10.27 (~RAS)
~RAS11: RP19.2 (R1.2), SIM11.27 (~RAS), SIM12.27 (~RAS)
~RAS13: RP19.8 (R4.2), SIM13.27 (~RAS), SIM14.27 (~RAS)
~RAS15: RP19.6 (R3.2), SIM15.27 (~RAS), SIM16.27 (~RAS)
~WE1: RP12.4 (R2.2), SIM1.21 (~WE), SIM2.21 (~WE)
~WE3: RP12.2 (R1.2), SIM3.21 (~WE), SIM4.21 (~WE)
~WE5: RP12.8 (R4.2), SIM5.21 (~WE), SIM6.21 (~WE)
~WE7: RP12.6 (R3.2), SIM7.21 (~WE), SIM8.21 (~WE)
~WE9: RP13.4 (R2.2), SIM9.21 (~WE), SIM10.21 (~WE)
~WE11: RP13.6 (R3.2), SIM11.21 (~WE), SIM12.21 (~WE)
~WE13: RP13.8 (R4.2), SIM13.21 (~WE), SIM14.21 (~WE)
~WE15: RP13.2 (R1.2), SIM15.21 (~WE), SIM16.21 (~WE)
~WE_M: S1.46, U10.2 (1A0), U10.4 (1A1), U10.6 (1A2), U10.8 (1A3), U10.11 (2A3), U10.13 (2A2), U10.15 (2A1), U10.17 (2A0)

Notes on the sheet:
Power pins on S1 edge connector need verifying against real hardware. Only 31, 62, 80, 98 are correct.
